AdrianChemicz/CAN-Eval-Board/CANFD_BoardHardware/CANFD_EvalBoard.sch

## KiCad design CANFD_BoardHardware/CANFD_EvalBoard.sch (2022-04-02)

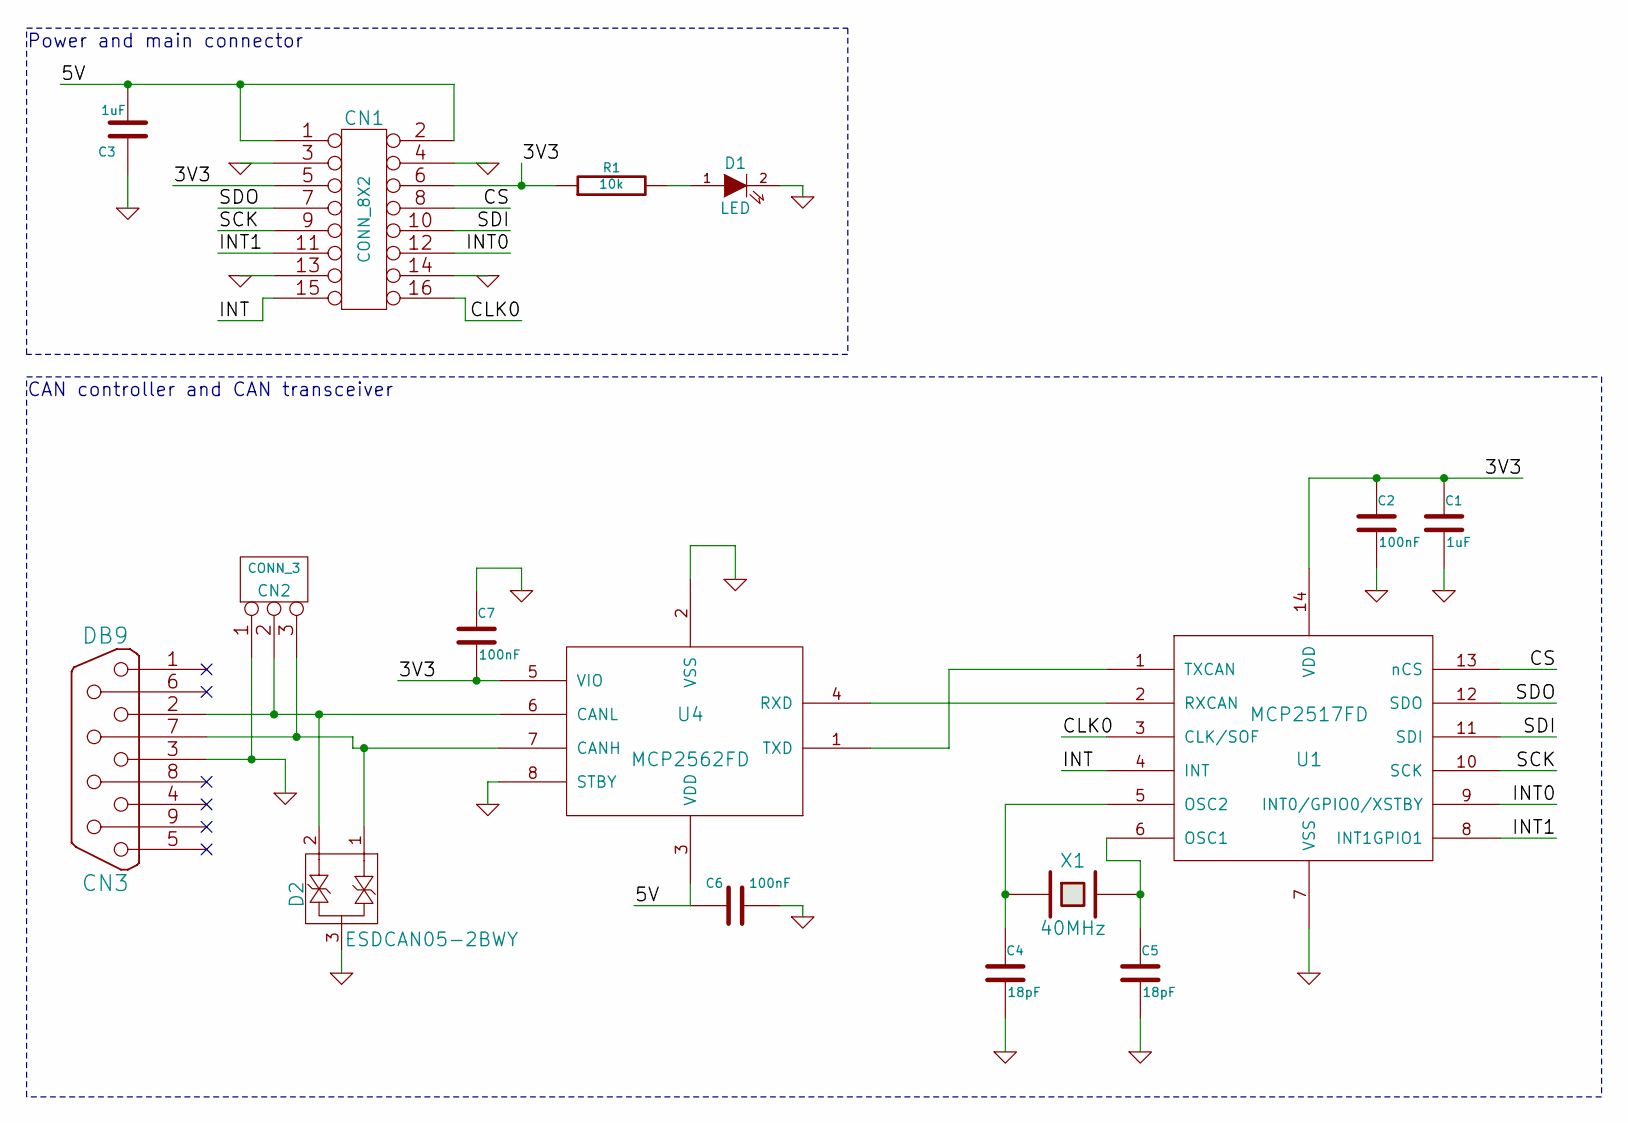
[picture p21: schematic CANFD_EvalBoard.sch]

Parts:
C1, C3: 1uF
C2, C6, C7: 100nF
C4, C5: 18pF
CN1: CONN_8X2
CN2: CONN_3
CN3: DB9
D1: LED
D2: ESDCAN05-2BWY
R1: 10k
U1: MCP2517FD
U4: MCP2562FD
X1: 40MHz

Connections:
3V3: C1.1, C2.1, C7.2, CN1.5, CN1.6, R1.1, U1.14 (VDD), U4.5 (VIO)
5V: C3.2, C6.1, CN1.1, CN1.2, U4.3 (VDD)
CLK0: CN1.16, U1.3 (CLK/SOF)
CS: CN1.8, U1.13 (nCS)
GND: C1.2, C2.2, C3.1, C4.2, C5.2, C6.2, C7.1, CN1.3, CN1.4, CN1.13, CN1.14, CN2.1, CN3.3, D1.2 (K), D2.3, U1.7 (VSS), U4.2 (VSS), U4.8 (STBY)
INT: CN1.15, U1.4 (INT)
INT0: CN1.12, U1.9 (INT0/GPIO0/XSTBY)
INT1: CN1.11, U1.8 (INT1GPIO1)
unnamed: C4.1, U1.5 (OSC2), X1.1
unnamed: C5.1, U1.6 (OSC1), X1.2
unnamed: CN2.2 (PM), CN3.2, D2.2, U4.6 (CANL)
unnamed: CN2.3, CN3.7, D2.1, U4.7 (CANH)
unnamed: D1.1 (A), R1.2
unnamed: U1.1 (TXCAN), U4.1 (TXD)
unnamed: U1.2 (RXCAN), U4.4 (RXD)
SCK: CN1.9, U1.10 (SCK)
SDI: CN1.10, U1.11 (SDI)
SDO: CN1.7, U1.12 (SDO)

Notes on the sheet:
Power and main connector
CAN controller and CAN transceiver
