AdrianChemicz/CAN-Eval-Board/CANFD_OptoIsolationBoardHardware/CANFD_OptoIsolationBoard.sch

## KiCad design CANFD_OptoIsolationBoardHardware/CANFD_OptoIsolationBoard.sch (2022-04-02, an earlier design)

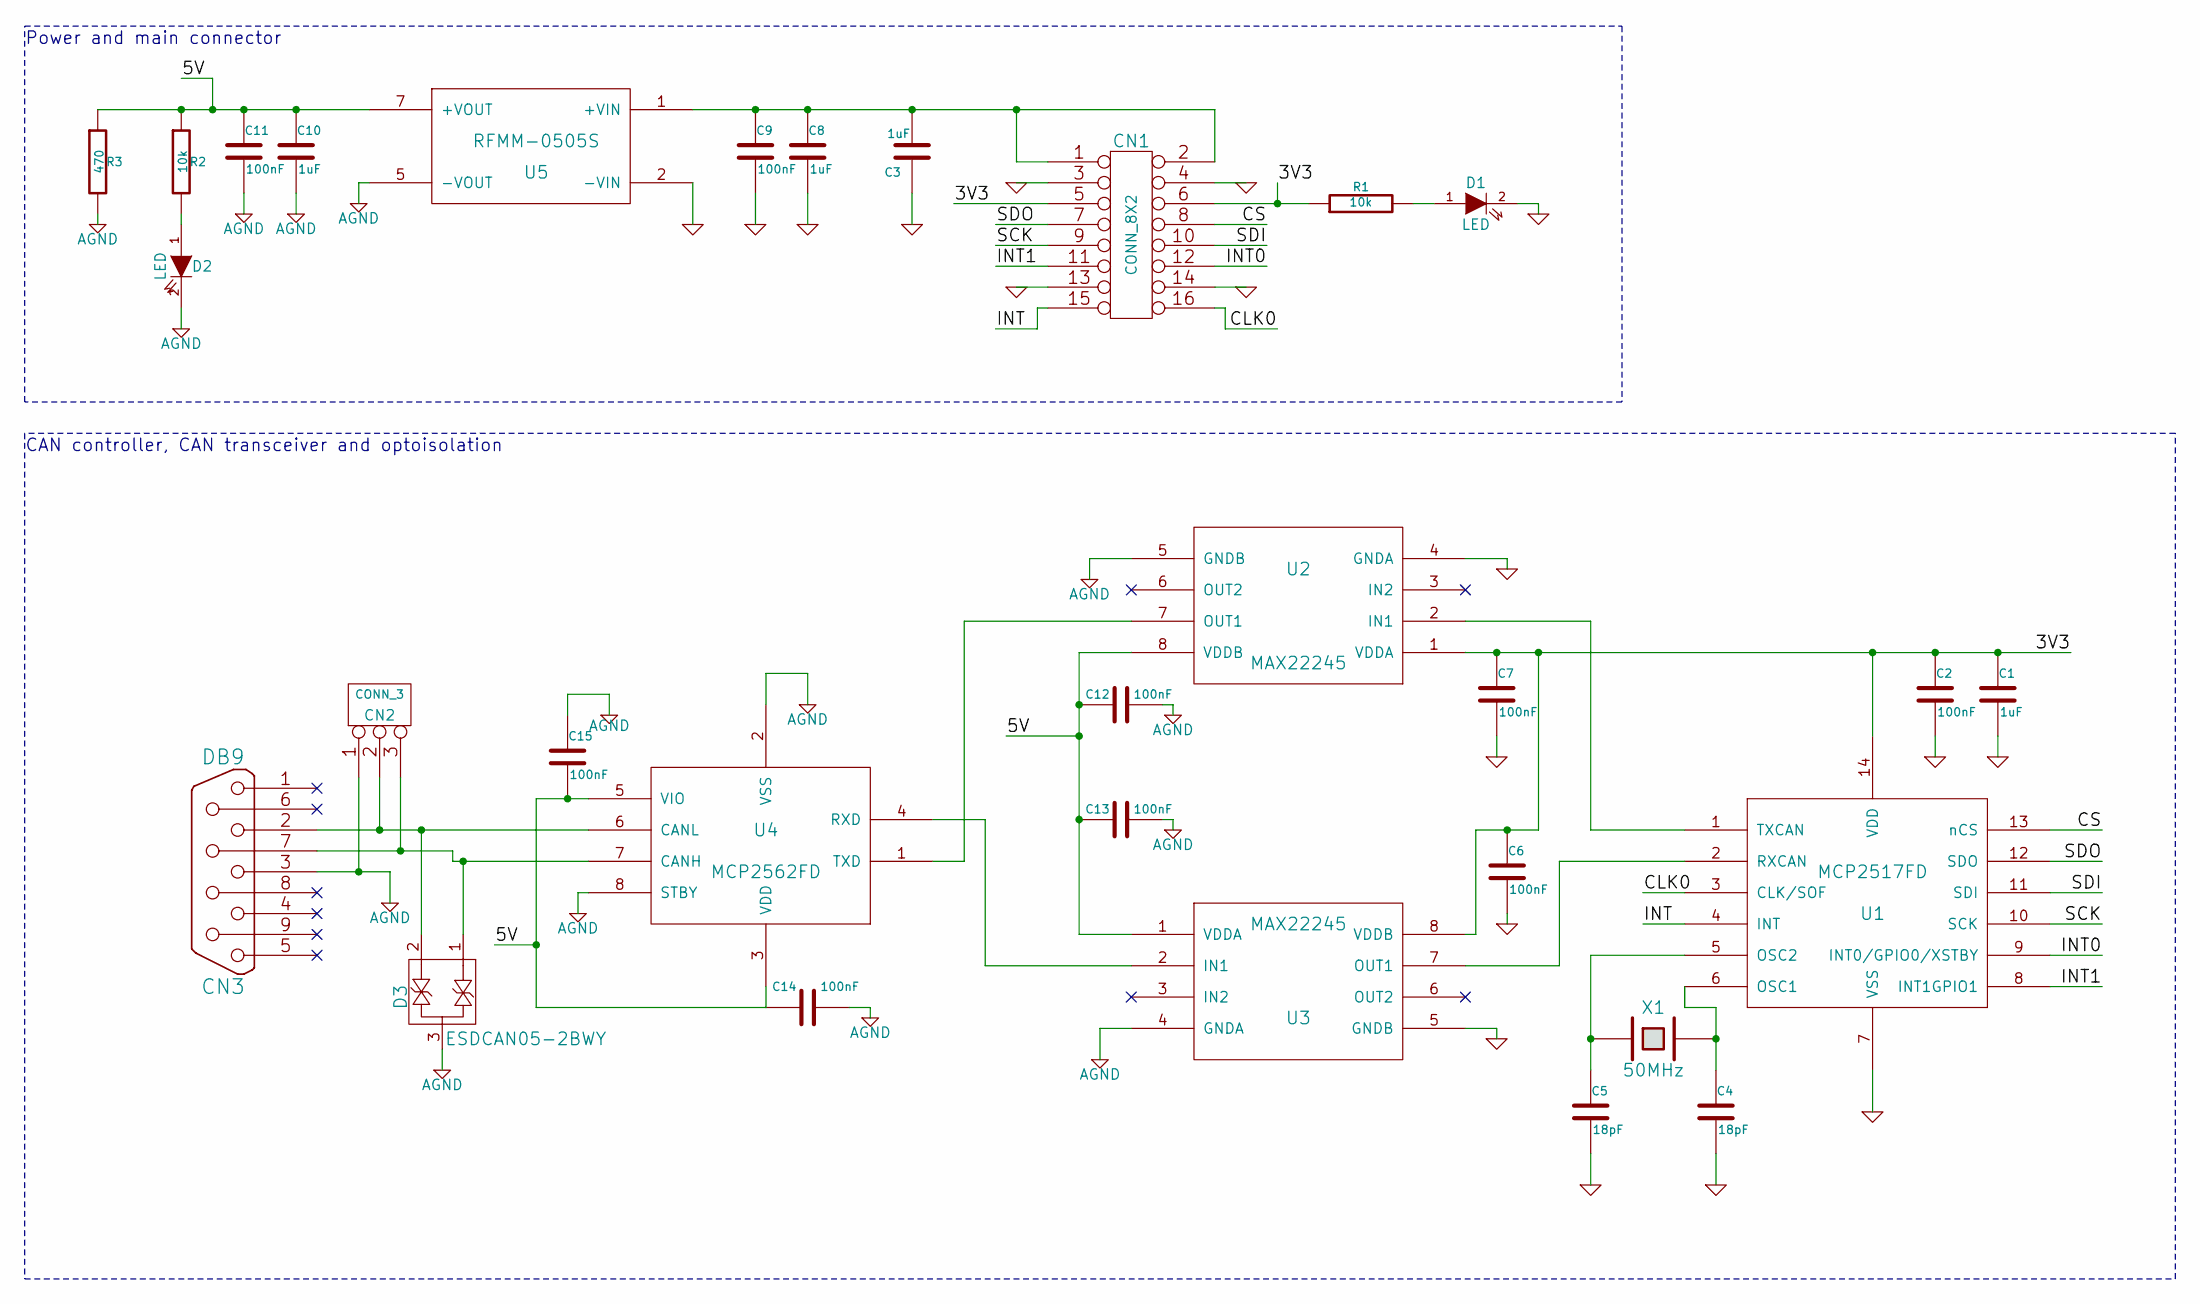
[picture p22: schematic CANFD_OptoIsolationBoard.sch]

Parts:
C1, C3, C8, C10: 1uF
C2, C6, C7, C9, C11, C12, C13, C14, C15: 100nF
C4, C5: 18pF
CN1: CONN_8X2
CN2: CONN_3
CN3: DB9
D1, D2: LED
D3: ESDCAN05-2BWY
R1, R2: 10k
R3: 470
U1: MCP2517FD
U2, U3: MAX22245
U4: MCP2562FD
U5: RFMM-0505S
X1: 50MHz

Connections:
3V3: C1.1, C2.1, C6.1, C7.1, CN1.5, CN1.6, R1.1, U1.14 (VDD), U2.1 (VDDA), U3.8 (VDDB)
5V: C10.1, C11.1, C12.1, C13.1, C14.1, C15.2, R2.1, R3.1, U2.8 (VDDB), U3.1 (VDDA), U4.3 (VDD), U4.5 (VIO), U5.7 (+VOUT)
AGND: C10.2, C11.2, C12.2, C13.2, C14.2, C15.1, CN2.1, CN3.3, D2.2 (K), D3.3, R3.2, U2.5 (GNDB), U3.4 (GNDA), U4.2 (VSS), U4.8 (STBY), U5.5 (-VOUT)
CLK0: CN1.16, U1.3 (CLK/SOF)
CS: CN1.8, U1.13 (nCS)
GND: C1.2, C2.2, C3.1, C4.2, C5.2, C6.2, C7.2, C8.2, C9.2, CN1.3, CN1.4, CN1.13, CN1.14, D1.2 (K), U1.7 (VSS), U2.4 (GNDA), U3.5 (GNDB), U5.2 (-VIN)
INT: CN1.15, U1.4 (INT)
INT0: CN1.12, U1.9 (INT0/GPIO0/XSTBY)
INT1: CN1.11, U1.8 (INT1GPIO1)
unnamed: C3.2, C8.1, C9.1, CN1.1, CN1.2, U5.1 (+VIN)
unnamed: C4.1, U1.6 (OSC1), X1.2
unnamed: C5.1, U1.5 (OSC2), X1.1
unnamed: CN2.2 (PM), CN3.2, D3.2, U4.6 (CANL)
unnamed: CN2.3, CN3.7, D3.1, U4.7 (CANH)
unnamed: D1.1 (A), R1.2
unnamed: D2.1 (A), R2.2
unnamed: U1.1 (TXCAN), U2.2 (IN1)
unnamed: U1.2 (RXCAN), U3.7 (OUT1)
unnamed: U2.7 (OUT1), U4.1 (TXD)
unnamed: U3.2 (IN1), U4.4 (RXD)
SCK: CN1.9, U1.10 (SCK)
SDI: CN1.10, U1.11 (SDI)
SDO: CN1.7, U1.12 (SDO)

Notes on the sheet:
Power and main connector
CAN controller, CAN transceiver and optoisolation
