AdrianChemicz/CAN-Eval-Board/LPC82X_EvalBoard/LPC82X_EvalBoard.sch

## KiCad design LPC82X_EvalBoard/LPC82X_EvalBoard.sch (2022-03-09)

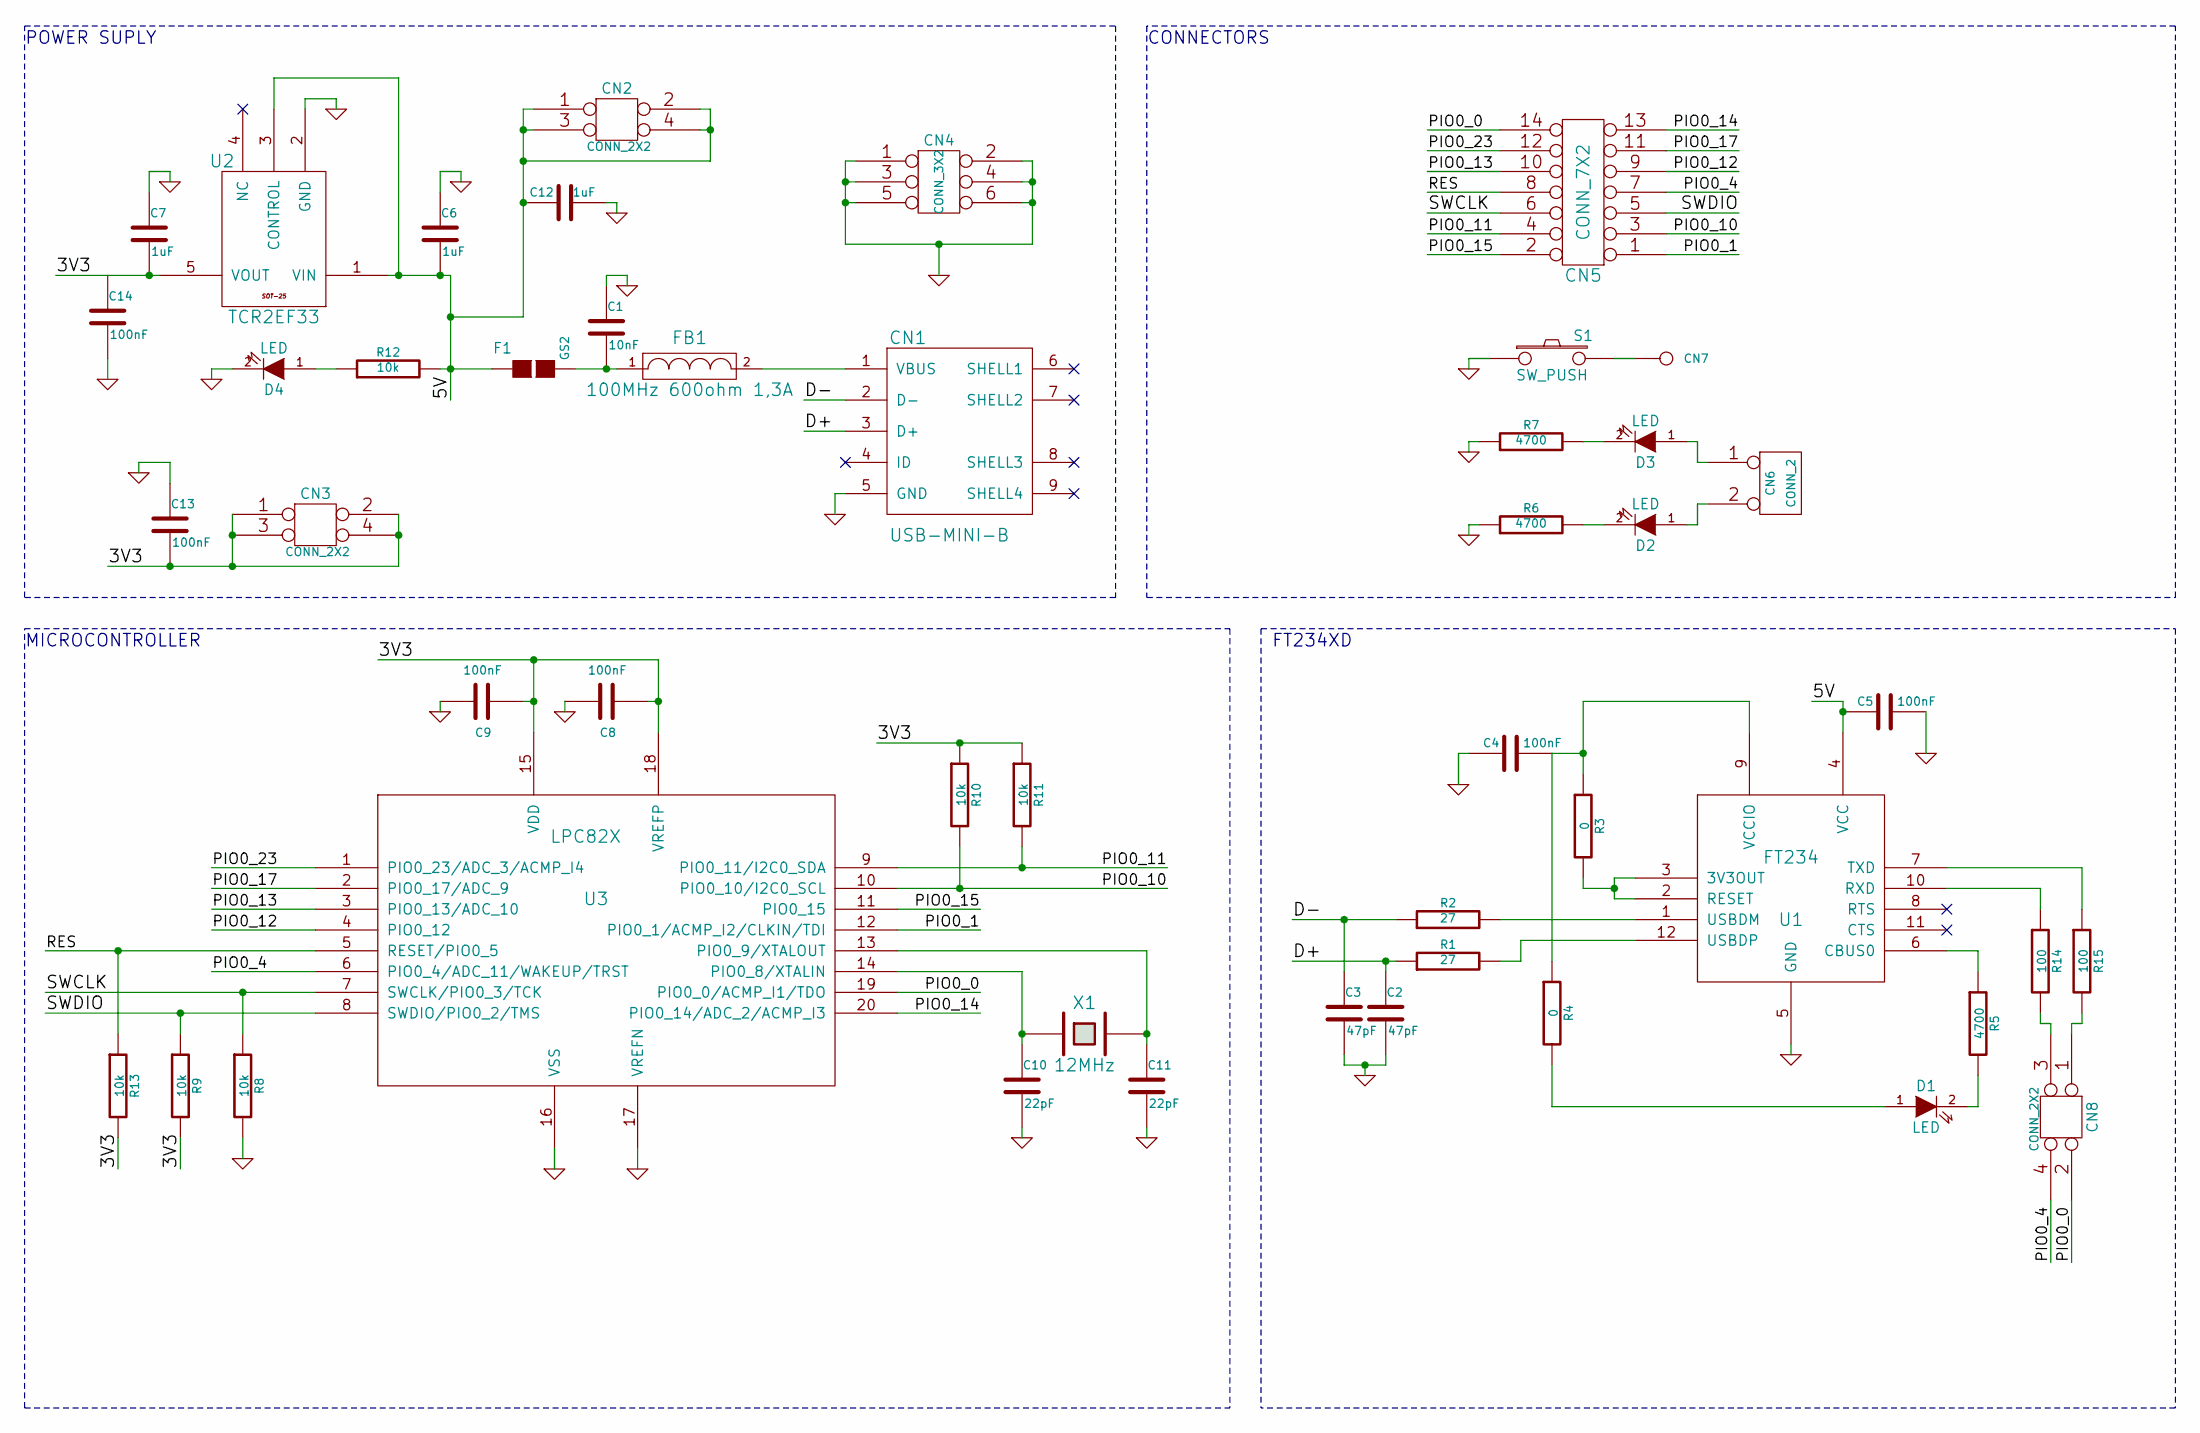
[picture p23: schematic LPC82X_EvalBoard.sch]

Parts:
C1: 10nF
C2, C3: 47pF
C4, C5, C8, C9, C13, C14: 100nF
C6, C7, C12: 1uF
C10, C11: 22pF
CN1: USB-MINI-B
CN2, CN3, CN8: CONN_2X2
CN4: CONN_3X2
CN5: CONN_7X2
CN6: CONN_2
CN7: CONN_1
D1, D2, D3, D4: LED
F1: GS2
FB1: 100MHz 600ohm 1,3A
R1, R2: 27
R3, R4: 0
R5, R6, R7: 4700
R8, R9, R10, R11, R12, R13: 10k
R14, R15: 100
S1: SW_PUSH
U1: FT234
U2: TCR2EF33
U3: LPC82X
X1: 12MHz

Connections:
3V3: C7.2, C8.2, C9.2, C13.2, CN3.1, CN3.2, CN3.3, CN3.4, R9.2, R10.1, R11.1, R13.2, U2.5 (VOUT), U3.15 (VDD), U3.18 (VREFP)
5V: C5.1, C6.2, C12.1, CN2.1, CN2.2, CN2.3, CN2.4, F1.1 (G1), R12.2, U1.4 (VCC), U2.1 (VIN), U2.3 (CONTROL)
D+: C2.1, CN1.3 (D+), R1.1
D-: C3.1, CN1.2 (D-), R2.1
GND: C1.1, C2.2, C3.2, C4.1, C5.2, C6.1, C7.1, C8.1, C9.1, C10.2, C11.2, C12.2, C13.1, C14.2, CN1.5 (GND), CN4.1, CN4.2, CN4.3, CN4.4, CN4.5, CN4.6, D4.2 (K), R6.1, R7.1, R8.2, S1.1, U1.5 (GND), U2.2 (GND), U3.16 (VSS), U3.17 (VREFN)
unnamed: C1.2, F1.2 (G2), FB1.1
unnamed: C4.2, R3.1, R4.1, U1.9 (VCCIO)
unnamed: C10.1, U3.14 (PIO0_8/XTALIN), X1.1
unnamed: C11.1, U3.13 (PIO0_9/XTALOUT), X1.2
unnamed: CN1.1 (VBUS), FB1.2
unnamed: CN6.1, D3.1 (A)
unnamed: CN6.2 (PM), D2.1 (A)
unnamed: CN7.1, S1.2
unnamed: CN8.1, R15.2
unnamed: CN8.3, R14.2
unnamed: D1.1 (A), R4.2
unnamed: D1.2 (K), R5.2
unnamed: D2.2 (K), R6.2
unnamed: D3.2 (K), R7.2
unnamed: D4.1 (A), R12.1
unnamed: R1.2, U1.12 (USBDP)
unnamed: R2.2, U1.1 (USBDM)
unnamed: R3.2, U1.2 (RESET), U1.3 (3V3OUT)
unnamed: R5.1, U1.6 (CBUS0)
unnamed: R14.1, U1.10 (RXD)
unnamed: R15.1, U1.7 (TXD)
PIO0_0: CN5.14, CN8.2, U3.19 (PIO0_0/ACMP_I1/TDO)
PIO0_1: CN5.1, U3.12 (PIO0_1/ACMP_I2/CLKIN/TDI)
PIO0_4: CN5.7, CN8.4, U3.6 (PIO0_4/ADC_11/WAKEUP/TRST)
PIO0_10: CN5.3, R10.2, U3.10 (PIO0_10/I2C0_SCL)
PIO0_11: CN5.4, R11.2, U3.9 (PIO0_11/I2C0_SDA)
PIO0_12: CN5.9, U3.4 (PIO0_12)
PIO0_13: CN5.10, U3.3 (PIO0_13/ADC_10)
PIO0_14: CN5.13, U3.20 (PIO0_14/ADC_2/ACMP_I3)
PIO0_15: CN5.2, U3.11 (PIO0_15)
PIO0_17: CN5.11, U3.2 (PIO0_17/ADC_9)
PIO0_23: CN5.12, U3.1 (PIO0_23/ADC_3/ACMP_I4)
RES: CN5.8, R13.1, U3.5 (RESET/PIO0_5)
SWCLK: CN5.6, R8.1, U3.7 (SWCLK/PIO0_3/TCK)
SWDIO: CN5.5, R9.1, U3.8 (SWDIO/PIO0_2/TMS)

Notes on the sheet:
POWER SUPLY
CONNECTORS
MICROCONTROLLER
FT234XD
